bhgv/nrf52832-eink-devboard/src/eink-2.9i-flex/User/e-Paper/ImageData.c

/*****************************************************************************
* | File      	:   ImageData.c
* | Author      :   Waveshare team
* | Function    :	
*----------------
* |	This version:   V1.0
* | Date        :   2018-10-23
* | Info        :
*
#
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

******************************************************************************/

#include "ImageData.h"



unsigned char gImage_2in7[5808]  = { 
/* 0X00,0X01,0XB0,0X00,0X08,0X01, */
0XFF,0XFF,0XFF,0XFF,0XFF,0XFF,0XFF,0XFF,0XFE,0X1F,0XFF,0XFF,0XFF,0XFF,0XFF,0XFF,
0XE1,0XFF,0XFF,0XFF,0XFF,0XFF,0XFF,0XFF,0XFF,0XFF,0XFF,0XFF,0XFF,0XFF,0XFE,0X1F,
0XFF,0XFF,0XFF,0XFF,0XFF,0XFF,0XE1,0XFF,0XFF,0XFF,0XFF,0XFF,0XFF,0XFF,0XFF,0XFF,
0XFF,0XFF,0XFF,0XFF,0XFE,0X1F,0XFF,0XFF,0XFF,0XFF,0XFF,0XFF,0XE1,0XFF,0XFF,0XFF,
0XFF,0XFF,0XFF,0XFF,0XFF,0XFF,0XFF,0XFF,0XFF,0XFF,0XFE,0X1F,0XFF,0XFF,0XFF,0XFF,
0XFF,0XFF,0XE1,0XFF,0XFF,0XFF,0XFF,0XFF,0XFF,0XFF,0XFF,0XFF,0XFF,0XFF,0XFF,0XFF,
0XFE,0X1F,0XFF,0XFF,0XFF,0XFF,0XFF,0XFF,0XE1,0XFF,0XFF,0XFF,0XFF,0XFF,0XFF,0XFF,
0XFF,0XFF,0XFF,0XFF,0XFF,0XFF,0XFE,0X1F,0XFF,0XFF,0XFF,0XFF,0XFF,0XFF,0XE1,0XFF,
0XFF,0XFF,0XFF,0XFF,0XFF,0XFF,0XFF,0XFF,0XFF,0XFF,0XFF,0XFF,0XFE,0X1F,0XFF,0XFF,
0XFF,0XFF,0XFF,0XFF,0XE1,0XFF,0XFF,0XFF,0XFF,0XFF,0XFF,0XFF,0XFF,0XFF,0XFF,0XFF,
0XFF,0XFF,0XFE,0X1F,0XFF,0XFF,0XFF,0XFF,0XFF,0XFF,0XE1,0XFF,0XFF,0XFF,0XFF,0XFF,
0XFF,0XFF,0XFF,0XFF,0XFF,0XFF,0XFF,0XFF,0XFE,0X1F,0XFF,0XFF,0XFF,0XFF,0XFF,0XFF,
0XE1,0XFF,0XFF,0XFF,0XFF,0XFF,0XFF,0XFF,0XFF,0XFF,0XFF,0XFF,0XFF,0XFF,0XFE,0X1F,
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
0XFF,0XFF,0XFF,0XFF,0XFF,0XFF,0XFF,0XFF,0XFF,0XFF,0XFF,0XFF,0XFE,0X1F,0XFF,0XFF,
0XFF,0XFF,0XFF,0XFF,0XE1,0XFF,0XFF,0XFF,0XFF,0XFF,0XFF,0XFF,0XFF,0XFF,0XFF,0XFF,
0XFF,0XFF,0XFE,0X1F,0XFF,0XFF,0XFF,0XFF,0XFF,0XFF,0XE1,0XFF,0XFF,0XFF,0XFF,0XFF,
};
